hardware-x/UntamedDataLogger/images/photo_2025-04-24_19-03-49.jpg

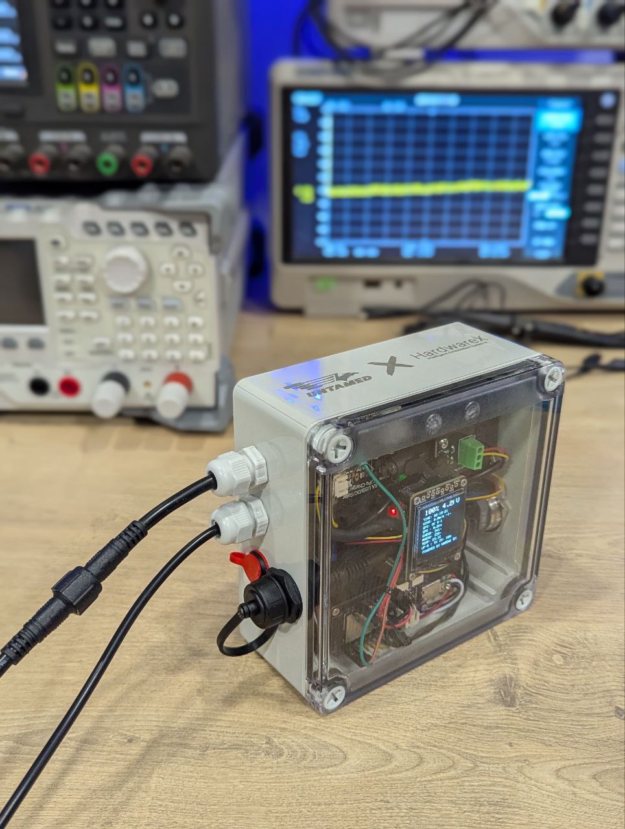
images/photo_2025-04-24_19-03-49.jpg
