hardware-x/UntamedDataLogger/images/photo_2025-04-24_19-03-50.jpg

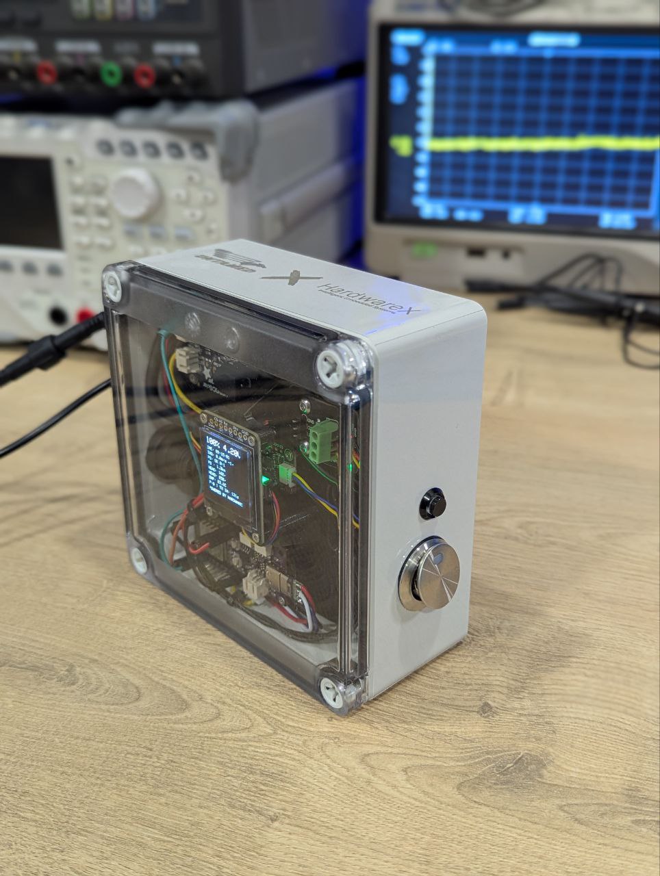
images/photo_2025-04-24_19-03-50.jpg
