hardware-x/UntamedDataLogger/images/photo_2025-04-24_19-03-52.jpg

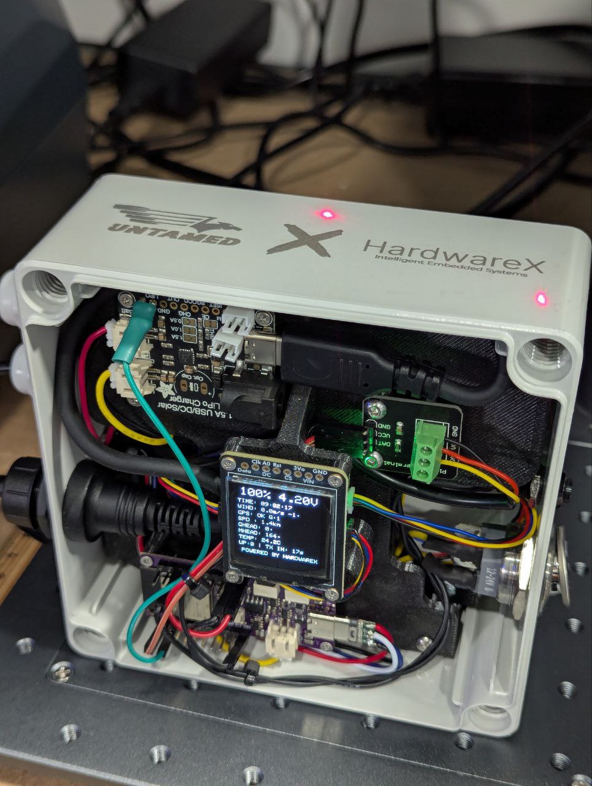
images/photo_2025-04-24_19-03-52.jpg
